Xevi8X/PCB-etcher/source_code/src/controller.cpp

#include "Arduino.h"

#include "controller.hpp"
#include "config.h"
#include "program_state.h"
#include "myEEPROM.hpp"

typedef struct PID_data_t
{
    float integral = 0.0f;
    float last_val = FLT_MAX;
} PID_data_t;

extern State state;
PID_data_t pid_data;


void bangBangController()
{
  if(state.status != ProgramStatus::WORKING)
  {
    state.power = 0;
    return;
  }

  float error = state.targetTemp - state.actualTemp;

  if(state.power != 255  && error > state.controller_param.hysteresis)
  {
     state.power = 255;
     return;
  }
  if(state.power != 0 && error < -state.controller_param.hysteresis)
  {
     state.power = 0;
     return;
  }
}

void PID_Controller()
{
  if(state.status != ProgramStatus::WORKING)
  {
    state.power = 0;
    return;
  }

  float error = state.targetTemp - state.actualTemp; 
  //P
  float tmp = state.controller_param.Kp * error; 
  //I
  bool I_action = fabs(error) < I_ACTION_RANGE;
  float dI;
  if(I_action)
  {
    dI = error * MEASURE_PERIOD_IN_MILLIS/1000.0f;
    pid_data.integral += dI;
    tmp += state.controller_param.Ki*pid_data.integral;
  }
  else pid_data.integral = 0.0f;
  //D
  if(pid_data.last_val != FLT_MAX && state.controller_param.Kd != 0.0f)
  {
    tmp += state.controller_param.Kd* (error-pid_data.last_val)*1000.0f/MEASURE_PERIOD_IN_MILLIS;
  }
  pid_data.last_val = error;
  

  //SATURATION
  int newPower = (int)tmp;
  bool overshoot = false;
  if(newPower > 255)
  {
    overshoot= true;
    newPower = 255;
  }
  if(newPower < 0)
  {
    overshoot= true;
    newPower = 0;
  }

  //ANTI-WINDUP - CLAMPING
  if(I_action && state.controller_param.antyWindUp && overshoot)
  {
    if((error > 0 && newPower == 255) || (error < 0 && newPower == 0))
    pid_data.integral -= dI;
  }

  state.power = newPower;
}

void initControllers()
{
  getControllerParams();

  // state.controller_param.Kp = Kp_init;
  // state.controller_param.Ki = Ki_init;
  // state.controller_param.Kd = Kd_init;
  // state.controller_param.hysteresis = Hysteresis_init;
  // state.controller_param.antyWindUp = false;
}

void controllerWork()
{
  switch (state.controller)
  {
    case Controllers::NONE:
      break;

    case Controllers::BANG_BANG:
      bangBangController();
      break;

    case Controllers::PID:
      PID_Controller();
      break;
  }
}

void clearControllers()
{
  //Bang-bang
  //Nothing to clean
  //PID
  pid_data.integral = 0.0f;
  pid_data.last_val = FLT_MAX;
}
