Xevi8X/PCB-etcher/source_code/include/controller.hpp

#include <float.h>

//Configuration
//==================================================

//BANG-BANG
#define Hysteresis_init 1.0f

//PID
#define Kp_init 1.0f
#define Ki_init 0.1f
#define Kd_init 0.1f

//==================================================


void initControllers();
void controllerWork();
void clearControllers();
