Xevi8X/PCB-etcher/source_code/include/config.h

//Configuration
//==================================================
#define MEASURE_PERIOD_IN_MILLIS 500
#define OVERHEAT_PROTECTION 60.0f
#define I_ACTION_RANGE 3.0f
//==================================================
